robin48gx/TH7/kicad/IMG_20180930_121822.jpg

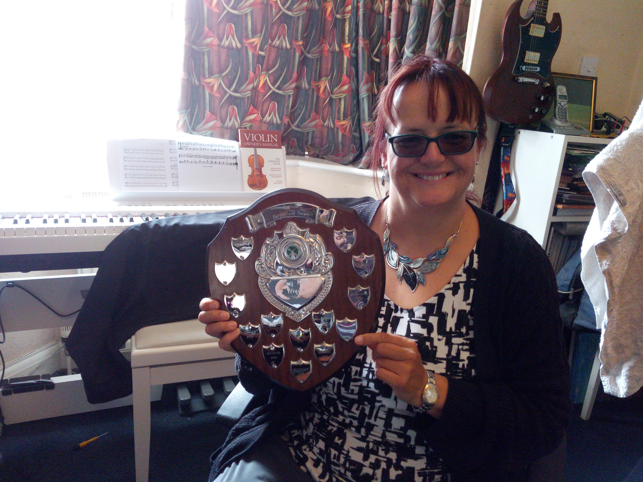
kicad/IMG_20180930_121822.jpg
